Uspizig/SensePuck/images/IMG_20250218_082801.jpg

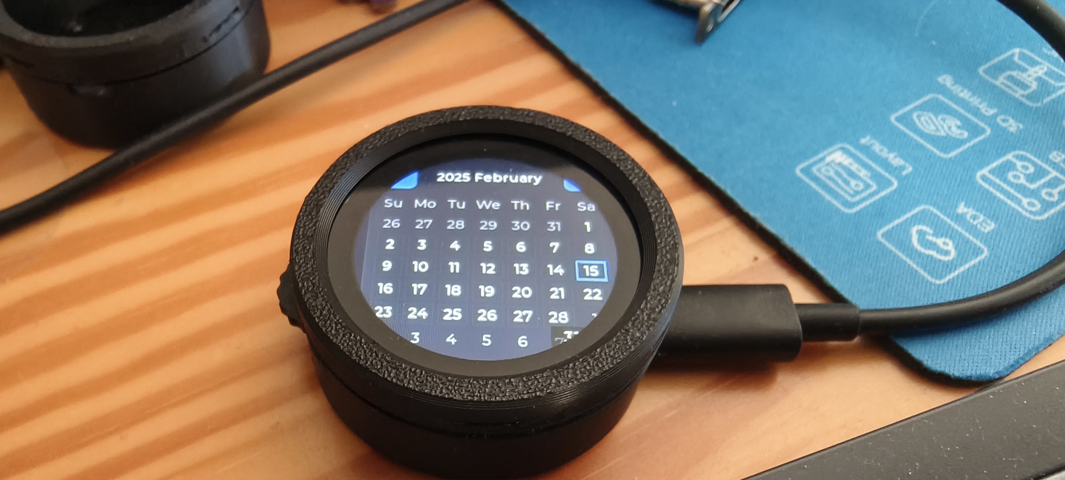
images/IMG_20250218_082801.jpg
