Uspizig/SensePuck/software/modular2/Rotary.cpp

#include "Rotary.h"

AiEsp32RotaryEncoder rotaryEncoder = AiEsp32RotaryEncoder(ROTARY_ENCODER_A_PIN, ROTARY_ENCODER_B_PIN, ROTARY_ENCODER_BUTTON_PIN, ROTARY_ENCODER_VCC_PIN, ROTARY_ENCODER_STEPS);

void IRAM_ATTR readEncoderISR() {
  rotaryEncoder.readEncoder_ISR();
}

void rotary_setup(void){
  pinMode(ROTARY_ENCODER_A_PIN, INPUT_PULLUP);
  pinMode(ROTARY_ENCODER_B_PIN, INPUT_PULLUP);

  //we must initialize rotary encoder
  rotaryEncoder.begin();
  rotaryEncoder.setup(readEncoderISR);
  //set boundaries and if values should cycle or not
  //in this example we will set possible values between 0 and 1000;
  bool circleValues = false;
  rotaryEncoder.setBoundaries(0, MAX_ROTARY_VALUE, circleValues);  //minValue, maxValue, circleValues true|false (when max go to min and vice versa)

  /*Rotary acceleration introduced 25.2.2021.
   * in case range to select is huge, for example - select a value between 0 and 1000 and we want 785
   * without accelerateion you need long time to get to that number
   * Using acceleration, faster you turn, faster will the value raise.
   * For fine tuning slow down.
   */
  rotaryEncoder.disableAcceleration(); //acceleration is now enabled by default - disable if you dont need it
  //rotaryEncoder.setAcceleration(250);  //or set the value - larger number = more accelearation; 0 or 1 means disabled acceleration

}

void rotary_loop() {
  //dont print anything unless value changed
  if (rotaryEncoder.encoderChanged()) {
    USBSerial.print("Value: ");
    USBSerial.println(rotaryEncoder.readEncoder());
    audio.setVolume(rotaryEncoder.readEncoder());
  }
  handle_rotary_button();
}

void handle_rotary_button() {
  static unsigned long lastTimeButtonDown = 0;
  static bool wasButtonDown = false;

  bool isEncoderButtonDown = rotaryEncoder.isEncoderButtonDown();
  //isEncoderButtonDown = !isEncoderButtonDown; //uncomment this line if your button is reversed

  if (isEncoderButtonDown) {
    USBSerial.print("+");  //REMOVE THIS LINE IF YOU DONT WANT TO SEE
    if (!wasButtonDown) {
      //start measuring
      lastTimeButtonDown = millis();
    }
    //else we wait since button is still down
    wasButtonDown = true;
    return;
  }

  //button is up
  if (wasButtonDown) {
    USBSerial.println("");  //REMOVE THIS LINE IF YOU DONT WANT TO SEE
    //click happened, lets see if it was short click, long click or just too short
    if (millis() - lastTimeButtonDown >= longPressAfterMiliseconds) {
      on_button_long_click();
    } else if (millis() - lastTimeButtonDown >= shortPressAfterMiliseconds) {
      on_button_short_click();
    }
  }
  wasButtonDown = false;
}




void on_button_short_click() {
  USBSerial.print("button SHORT press ");
  USBSerial.print(millis());
  USBSerial.println(" milliseconds after restart");
}

void on_button_long_click() {
  USBSerial.print("button LONG press ");
  USBSerial.print(millis());
  USBSerial.println(" milliseconds after restart");
}
