Uspizig/SensePuck/software/modular2/audio_player.h

#pragma once
#ifndef _AUDIO_PLAYER_H
#define _AUDIO_PLAYER_H

#include <Arduino.h>
#include "io_pins.h"
#include "global.h"
//#include "Audio.h"
#include "TFTDisplay.h"
  


void setup_audio(void);

#endif
